jakplugg/Orgone-accumulator/orgone_accumulator/orgone_accumulator_2.0/orgone_accumulator_2.0.ino

/*
Copyright (c) <2016> <James L Matheson>

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
Neutron-sound.com
Orgone Accumulator 2.0
*/
//use 144mhz version, this version is no longer updated.

//pre 2.0 firmware orgones
//use config.h tab to change FX function button to momentary if you changed it.
//tune lock is now pulsar mode. you can change it back in config, but you get no pulsar mode.

//detune = FX
//detune prime = FX select
//detune enable = FX enable
//lock = pulsar

#include <stdint.h>
#include <Bounce.h>
#include <EEPROM.h>
#include "config.h"
#include <Arduino.h>

const float equalTemprementTable[] = {1, 1, 1.05946, 1.12246, 1.18921, 1.25992, 1.33483, 1.41421, 1.49831, 1.58740, 1.68179, 1.78180, 1.88775, 2};
const float justTable[] = {1, 1, 1.0417, 1.1250, 1.2, 1.25, 1.33333, 1.4063, 1.5, 1.6, 1.66666, 1.8, 1.875, 2};

const uint8_t smoothStepTable[] ={ 0,1,1,3,3,5,5,7,7,9,9,11,11,13,13,15};

const uint16_t HARM_LEVELS[] = { //for spectrum FX each row of 9 must add to around 4095 they are ROOT FIFTH OCTAVE 3RDHARM 4thHARM 5thHARM 6thHARM 7thHARM 8thHARM
  2047, 1027, 509, 257, 127, 65, 31, 17, 5, //used odd numbers because the number also determines the detune rate for that oscillator.
  2047, 255, 1027, 125, 509, 0, 0, 231, 512, //octaves
  2040, 0, 0, 0, 1023, 513, 511, 0, 7,
  1023, 0, 0, 0, 0, 1024, 1025, 1021, 0,
  1023, 0, 767, 511, 385, 255, 0, 129, 126,
  701, 102, 712, 256, 507, 64, 0, 511, 253,
  2048, 7, 15, 32, 65, 123, 255, 512, 1021,
  2047, 1024, 0, 1024, 0, 0, 0, 0, 0,
  1847, 1022, 0, 0, 1021, 64, 0, 62, 61,
  2047, 69, 2055, 67, 65, 64, 0, 62, 61,
  2047, 69, 68, 2041, 65, 64, 0, 62, 61,
  2047, 69, 68, 67, 2035, 64, 0, 62, 61,
  0, 0, 0, 0, 1020, 1021, 0, 1023, 1022,
  320, 1241, 321, 735, 1035, 0, 0, 0, 561,
  1803, 0, 168, 0, 504, 0, 1020, 0, 501,
  1703, 251, 0, 502, 307, 201, 0, 1001, 126,
};

const int16_t sinTable[] = {
  0, 402, 804, 1206, 1607, 2009, 2410, 2811, 3211, 3611, 4011, 4409, 4807, 5205, 5601, 5997, 6392,
  6786, 7179, 7571, 7961, 8351, 8739, 9126, 9511, 9895, 10278, 10659, 11038, 11416, 11792, 12166, 12539,
  12909, 13278, 13645, 14009, 14372, 14732, 15090, 15446, 15799, 16150, 16499, 16845, 17189, 17530, 17868, 18204,
  18537, 18867, 19194, 19519, 19840, 20159, 20474, 20787, 21096, 21402, 21705, 22004, 22301, 22594, 22883, 23169,
  23452, 23731, 24006, 24278, 24546, 24811, 25072, 25329, 25582, 25831, 26077, 26318, 26556, 26789, 27019, 27244,
  27466, 27683, 27896, 28105, 28309, 28510, 28706, 28897, 29085, 29268, 29446, 29621, 29790, 29955, 30116, 30272,
  30424, 30571, 30713, 30851, 30984, 31113, 31236, 31356, 31470, 31580, 31684, 31785, 31880, 31970, 32056, 32137,
  32213, 32284, 32350, 32412, 32468, 32520, 32567, 32609, 32646, 32678, 32705, 32727, 32744, 32757, 32764, 32767,
  32764, 32757, 32744, 32727, 32705, 32678, 32646, 32609, 32567, 32520, 32468, 32412, 32350, 32284, 32213, 32137,
  32056, 31970, 31880, 31785, 31684, 31580, 31470, 31356, 31236, 31113, 30984, 30851, 30713, 30571, 30424, 30272,
  30116, 29955, 29790, 29621, 29446, 29268, 29085, 28897, 28706, 28510, 28309, 28105, 27896, 27683, 27466, 27244,
  27019, 26789, 26556, 26318, 26077, 25831, 25582, 25329, 25072, 24811, 24546, 24278, 24006, 23731, 23452, 23169,
  22883, 22594, 22301, 22004, 21705, 21402, 21096, 20787, 20474, 20159, 19840, 19519, 19194, 18867, 18537, 18204,
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
    -30069,-29844,-29613,-29374,-29130,-28878,-28617,-28353,-28078,-27797,-27510,-27215,-26912,-26602,-26284,-25957,
    -25623,-25279,-24927,-24564,-24193,-23811,-23417,-23012,-22595,-22165,-21721,-21261,-20786,-20294,-19784,-19259,
    -18724,-18186,-17653,-17128,-16618,-16122,-15645,-15188,-14748,-14326,-13923,-13535,-13164,-12808,-12466,-12138,
    -11821,-11518,-11224,-10941,-10667,-10403,-10148,-9900,-9660,-9427,-9202,-8983,-8771,-8564,-8363,-8166,
    -7975,-7789,-7607,-7429,-7255,-7086,-6920,-6758,-6599,-6442,-6290,-6141,-5994,-5848,-5706,-5566,
    -5429,-5294,-5161,-5028,-4899,-4771,-4645,-4521,-4398,-4276,-4156,-4037,-3918,-3802,-3686,-3571,
    -3457,-3344,-3231,-3120,-3009,-2898,-2788,-2679,-2569,-2461,-2352,-2242,-2135,-2028,-1919,-1811,
    -1703,-1595,-1486,-1378,-1268,-1159,-1049,-939,-828,-718,-605,-491,-378,-263,-150,-30
};
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
