jakplugg/Orgone-accumulator/orgone_accumulator/orgone_accumulator_2.0/ASSIGNINCREMENTS.ino

void INCREMENT_PWM(){
  oSQ.phase_increment = (inputConverter / PWM_Div) * 4;
  oSQ.PW = (constrain(((FMIndexCont + (1024-(aInModIndex>>2))) ), 0, (2047-PWM_Min)))<<4;
}

void ASSIGNINCREMENTS() { //--------------------------------------------------------default

  CZMix = constrain((FMIndexCont + (2047 - (averageaInIAv / 2.0))), 0, 2047); 
  INCREMENT_PWM();
  switch (oscMode) { //switches which oscs get changed by FM and how much multiplier ;
    case 0://break intentionally ommited

      UPDATECONTROLS_FM();


      FMIndexContCubing = FMIndexCont / 256.0;
      FMIndex = (uint32_t((float)(((FMIndexContCubing * FMIndexContCubing * FMIndexContCubing) + (averageaInIAvCubing * averageaInIAvCubing * averageaInIAvCubing)) * (inputVOct / 2.0))));

      if (averageaInRAv > 4095) {
        ModRatioCubing = (averageaInRAv - 4095.0) / 256.0;
        aInModRatio = ((ModRatioCubing * ModRatioCubing * ModRatioCubing) / 2048.0) + 1.0;
      }
      else aInModRatio = (averageaInRAv / 4096.0); //down direction dont go past zero, or divide by zero could happen

      if (FMFixedOn) {
        avgcubing = (float)(averageratio / 500.0); //change to adjust "LFO" in fm fixed
        FMMult = ((((float)(avgcubing * avgcubing * avgcubing))) + 0.001) * (aInModRatio * 8.0); //FM+fixed mult control
        //Serial.println(FMMult);
        osc_mult[0] = FMMult;
        osc_mult[1] = 4.0;
        o2.phase_increment = inputConverter * osc_mult[1]  ;
        o4.phase_increment = (inputConverter  * chord[0] * osc_mult[1]) + detune[0];
        o6.phase_increment = (inputConverter  * chord[1] * osc_mult[1]) + detune[1];
        o8.phase_increment = (inputConverter * chord[2] * osc_mult[1]) + detune[2];
        o10.phase_increment =(inputConverter * chord[3] * osc_mult[1]) + detune[3];
        o1.phase_increment = inputConverterF * osc_mult[0] ;
        o3.phase_increment = (inputConverterF   * osc_mult[0])  + detune[0];
        o5.phase_increment = (inputConverterF   * osc_mult[0])  + detune[1];
        o7.phase_increment = (inputConverterF  * osc_mult[0])  + detune[2];
        o9.phase_increment = (inputConverterF   * osc_mult[0])  + detune[3];
        //lfo.phase_increment = inputConverterF * (osc_mult[0] / 8.0);
      }
      else {
        FMMult = ((int)((averageratio >> 8) + 1))/2.0 * aInModRatio; //FM + free
        osc_mult[0] = FMMult;
        osc_mult[1] = 4.0;
        o2.phase_increment = inputConverter * osc_mult[1]  ;
        o4.phase_increment = ((inputConverter ) * chord[0] * osc_mult[1]) + detune[0];
        o6.phase_increment = ((inputConverter ) * chord[1] * osc_mult[1]) + detune[1];
        o8.phase_increment = ((inputConverter ) * chord[2] * osc_mult[1]) + detune[2];
        o10.phase_increment = (( inputConverter) * chord[3] * osc_mult[1]) + detune[3];
        o1.phase_increment = inputConverter * osc_mult[0] ;
        o3.phase_increment = (inputConverter  * chord[0] * osc_mult[0])  + detune[0];
        o5.phase_increment = (inputConverter  * chord[1] * osc_mult[0])  + detune[1];
        o7.phase_increment = (inputConverter  * chord[2] * osc_mult[0])  + detune[2];
        o9.phase_increment = (inputConverter  * chord[3] * osc_mult[0])  + detune[3];
        //lfo.phase_increment = inputConverter * (osc_mult[0] / 4.0);
      }
      break;



    case 2://fm mode with x button pressed allows pitch bending on hi position and FM is LFO in fixed (no auto get freq).


      UPDATECONTROLS_FMALT();


      FMIndexContCubing = FMIndexCont / 256.0;
      FMIndex = (uint32_t((float)(((FMIndexContCubing * FMIndexContCubing * FMIndexContCubing) + (averageaInIAvCubing * averageaInIAvCubing * averageaInIAvCubing)) * (inputVOct/2.0))));

      if (averageaInRAv > 4095) {
        ModRatioCubing = (averageaInRAv - 4095) / 256.0;
        aInModRatio = ((ModRatioCubing * ModRatioCubing * ModRatioCubing) / 512.0) + 1.0;
      }
      else aInModRatio = (averageaInRAv / 4096.0); //down direction dont go past zero, or divide by zero could happen


      if (FMFixedOn) {
        float avgcubing = averageratio / 500.0; //change to adjust "LFO" in fm fixed
        FMMult = ((((float)(avgcubing * avgcubing * avgcubing))) + 0.001) * (aInModRatio * 8.0); //FM+fixed mult control
        osc_mult[0] = FMMult;
        osc_mult[1] = 4;
        FMX_HiOffset = (float)(1.0 + (mixHi * FMX_HiOffsetCont)/2048.0);
        o2.phase_increment = inputConverter * osc_mult[1] * FMX_HiOffset ;
        o4.phase_increment = inputConverter * chord[0]  * osc_mult[1] * FMX_HiOffset + detune[0] ;
        o6.phase_increment = inputConverter  * chord[1] * osc_mult[1]  * FMX_HiOffset + detune[1] ;
        o8.phase_increment = inputConverter  * chord[2] * osc_mult[1] * FMX_HiOffset + detune[2] ;
        o10.phase_increment = inputConverter * chord[3] * osc_mult[1] * FMX_HiOffset + detune[3] ;
        o1.phase_increment = inputConverterF  * osc_mult[0] ;
        o3.phase_increment = inputConverterF  * osc_mult[0] ;
        o5.phase_increment = inputConverterF * osc_mult[0] ;
        o7.phase_increment = inputConverterF * osc_mult[0] ;
        o9.phase_increment = inputConverterF * osc_mult[0] ;
        //lfo.phase_increment = inputConverterF * (osc_mult[0] / 8.0);
      }
      else {
        FMMult = ((int)((averageratio >> 9) + 1)) * aInModRatio; //FM + free
        osc_mult[0] = FMMult;
        osc_mult[1] = 4;
        FMX_HiOffset = (float)(1.0 + ((float)(mixHi) * FMX_HiOffsetCont)/2048.0);
        o2.phase_increment = inputConverter * osc_mult[1] * FMX_HiOffset ;
        o4.phase_increment = inputConverter * osc_mult[1] * chord[0] * FMX_HiOffset+ detune[0] ;
        o6.phase_increment = inputConverter * osc_mult[1] * chord[1] * FMX_HiOffset  + detune[1] ;
        o8.phase_increment = inputConverter * osc_mult[1] * chord[2] * FMX_HiOffset + detune[2] ;
        o10.phase_increment = inputConverter * osc_mult[1] * chord[3] * FMX_HiOffset + detune[3] ;
        o1.phase_increment = inputConverter * osc_mult[0] ;
        o3.phase_increment = inputConverter * osc_mult[0]  + detune[0];
        o5.phase_increment = inputConverter * osc_mult[0]  + detune[1];
        o7.phase_increment = inputConverter * osc_mult[0]  + detune[2];
        o9.phase_increment = inputConverter * osc_mult[0]  + detune[3];
        //lfo.phase_increment = inputConverter * (osc_mult[0] / 4.0);
      }
      break;
    case 1://cz

      UPDATECONTROLS_CZ();

      if (averageaInRAv > 4095) {
        ModRatioCubing = (averageaInRAv - 4095) / 256.0;
        aInModRatio = ((ModRatioCubing * ModRatioCubing * ModRatioCubing) / 2048.0) + 1.0;
      }
      else aInModRatio = (averageaInRAv / 4096.0); //down direction dont go past zero, or divide by zero could happen


      if (FMFixedOn) {
        FMMult = (float)((((averageratio >> 3) / 1.1)) + 1.0) * aInModRatio; 
        osc_mult[0] = 4;
        osc_mult[1] = FMMult;
       
        o1.phase_increment = inputConverter * osc_mult[0];
        o3.phase_increment = inputConverter * chord[0] * osc_mult[0] + detune[0];
        o5.phase_increment = inputConverter * chord[1] * osc_mult[0] + detune[1];
        o7.phase_increment = inputConverter * chord[2] * osc_mult[0] + detune[2];
        o9.phase_increment = inputConverter * chord[3] * osc_mult[0] + detune[3];
         o2.phase_increment =
          o4.phase_increment =
            o6.phase_increment =
              o8.phase_increment =
                o10.phase_increment = inputConverterA * osc_mult[1];
      }
      else {
        FMMult = (float)((((averageratio >> 5) / 7.0)) + 1.0) * aInModRatio; 
        osc_mult[0] = 4;
        osc_mult[1] = FMMult;        
        o2.phase_increment = inputConverter * osc_mult[1];
        o4.phase_increment = o2.phase_increment  * chord[0] + detune[0];
        o6.phase_increment = o2.phase_increment * chord[1] + detune[1];
        o8.phase_increment = o2.phase_increment  * chord[2] + detune[2];
        o10.phase_increment = o2.phase_increment  * chord[3] + detune[3];
        o1.phase_increment = inputConverter * osc_mult[0];
        o3.phase_increment = o1.phase_increment  * chord[0] + detune[0];
        o5.phase_increment = o1.phase_increment  * chord[1] + detune[1];
        o7.phase_increment = o1.phase_increment  * chord[2] + detune[2];
        o9.phase_increment = o1.phase_increment  * chord[3] + detune[3];
      }
      break;


    case 3://ALT CZ


      UPDATECONTROLS_CZALT();

     if (averageaInRAv > 4095) {
        ModRatioCubing = (averageaInRAv - 4095) / 256.0;
        aInModRatio = ((ModRatioCubing * ModRatioCubing * ModRatioCubing) / 2048.0) + 1.0;
      }
      else aInModRatio = (averageaInRAv / 4096.0); //down direction dont go past zero, or divide by zero could happen



      if (FMFixedOn) {
        FMMult = (float)((((averageratio >> 3) / 1.1)) + 1.0) * aInModRatio; //CZ + fixed + free
        osc_mult[0] = 4;
        osc_mult[1] = FMMult;
        FMX_HiOffset = (float)(1.0 + ((float)(mixHi) * FMX_HiOffsetCont)/2048.0);
        o2.phase_increment =  inputConverterA * osc_mult[1]*FMX_HiOffset;
        o4.phase_increment =  inputConverterA * chord[0] * osc_mult[1]*FMX_HiOffset;
        o6.phase_increment =  inputConverterA * chord[1] * osc_mult[1]*FMX_HiOffset;
        o8.phase_increment =  inputConverterA * chord[2] * osc_mult[1]*FMX_HiOffset;
        o10.phase_increment = inputConverterA * chord[3] * osc_mult[1]*FMX_HiOffset;
        o1.phase_increment = inputConverter * osc_mult[0]*FMX_HiOffset;
        o3.phase_increment = inputConverter * chord[0] * osc_mult[0]*FMX_HiOffset + detune[0];
        o5.phase_increment = inputConverter * chord[1] * osc_mult[0]*FMX_HiOffset + detune[1];
        o7.phase_increment = inputConverter * chord[2] * osc_mult[0]*FMX_HiOffset + detune[2];
        o9.phase_increment = inputConverter * chord[3] * osc_mult[0]*FMX_HiOffset + detune[3];
        lfo.phase_increment = inputConverterF * (osc_mult[1] / 8.0);
      }
      else {
        FMMult = (float)((((averageratio >> 5) / 7.0)) + 1.0) * aInModRatio;
        osc_mult[0] = 4;
        osc_mult[1] = FMMult;
        FMX_HiOffset = (float)(1.0 + ((float)(mixHi) * FMX_HiOffsetCont)/2048.0);
        o2.phase_increment = inputConverter * osc_mult[1];
        o4.phase_increment = o2.phase_increment  * chord[0] + detune[0];
        o6.phase_increment = o2.phase_increment * chord[1] + detune[1];
        o8.phase_increment = o2.phase_increment  * chord[2] + detune[2];
        o10.phase_increment = o2.phase_increment  * chord[3] + detune[3];
        o1.phase_increment = inputConverter * osc_mult[0]*FMX_HiOffset;
        o3.phase_increment = o1.phase_increment  * chord[0]*FMX_HiOffset + detune[0];
        o5.phase_increment = o1.phase_increment  * chord[1]*FMX_HiOffset + detune[1];
        o7.phase_increment = o1.phase_increment  * chord[2]*FMX_HiOffset + detune[2];
        o9.phase_increment = o1.phase_increment  * chord[3]*FMX_HiOffset + detune[3];
        lfo.phase_increment = inputConverter * (osc_mult[1] / 4.0);
      }

      break;

  }
}


void ASSIGNINCREMENTS_P() { //--------------------------------------------for pulsar

  PENV = PulsarEnv[analogControls[3] >> 9];

  FMIndexContCubing = FMIndexCont / 256.0;
   INCREMENT_PWM();
  switch (oscMode) { //switches which oscs get changed by FM and how much multiplier ;

    case 0:
      UPDATECONTROLS_FM();
       o1.phase_SUB = inputConverter * 1;
      FMX_HiOffset = 1;
      FMIndex = (uint32_t((float)(((FMIndexContCubing * FMIndexContCubing * FMIndexContCubing) + (averageaInIAvCubing * averageaInIAvCubing * averageaInIAvCubing)) * (inputVOct / 2.0))));
      break;
    case 1:
      UPDATECONTROLS_CZ();
      
      o1.phase_SUB = 0;
      FMX_HiOffset = 1;
      FMIndex = 0;
      break;
    case 2:
      UPDATECONTROLS_FMALT();
      o1.phase_SUB = inputConverter * 1;
      FMX_HiOffset = (float)(1.0 + ((float)(mixHi) * FMX_HiOffsetCont)/2048.0);
      FMIndex = (uint32_t((float)(((FMIndexContCubing * FMIndexContCubing * FMIndexContCubing) + (averageaInIAvCubing * averageaInIAvCubing * averageaInIAvCubing)) * (inputVOct / 2.0))));
      break;
    case 3:
      UPDATECONTROLS_CZALT();
      
      o1.phase_SUB = 0;
      FMX_HiOffset = (float)(1.0 + ((float)(mixHi) * FMX_HiOffsetCont)/2048.0);
      FMIndex = 0;
      break;
  }

  CZMix = 2047-(constrain((FMIndexCont + (2047 - (averageaInIAv / 2.0))), 0, 2020));//reverse control and offset pulse envelope length
  

  if (averageaInRAv > 4095) {
    ModRatioCubing = (averageaInRAv - 4095) / 256.0;
    aInModRatio = ((ModRatioCubing * ModRatioCubing * ModRatioCubing) / 512.0) + 1.0;
  }
  else aInModRatio = (averageaInRAv / 4096.0); 

  
   if (FMmodeOn){
  if (FMFixedOn) {
    
    if (FX == 6) FMMult = (float)((((analogControls[3]) * 1.5 )) + 1.0);
    else FMMult = (float)((((averageratio) >>1 )) + 1.0) * aInModRatio;
    osc_mult[0] = 4;
    osc_mult[1] = FMMult;
    osc_mult[2] = 4;

       
    o1.pulseAdd = (inputConverterF * osc_mult[2]) * (float)(CZMix / 6.0);

    o1.phase_increment = inputConverter * osc_mult[0] * FMX_HiOffset;
    o2.phase_increment = inputConverterF * osc_mult[1];
    o3.phase_increment = inputConverterF * osc_mult[2] + o1.pulseAdd;
    if (o1.phase_increment > (o3.phase_increment<<1))o3.phase_increment = o1.phase_increment>>1;//these stop the pulsar envelope getting longer than the pitch.

    o4.phase_increment = inputConverter   * chord[1] * osc_mult[0] * FMX_HiOffset + detune[1];
    o5.phase_increment = inputConverterF * osc_mult[1];
    o6.phase_increment = inputConverterF * osc_mult[2] + o1.pulseAdd;
    if (o4.phase_increment > (o6.phase_increment<<1))o6.phase_increment = o4.phase_increment>>1;

    o7.phase_increment = inputConverter  * chord[2] * osc_mult[0] * FMX_HiOffset + detune[2];
    o8.phase_increment = inputConverterF * osc_mult[1];
    o9.phase_increment = inputConverterF * osc_mult[2] + o1.pulseAdd;
    if (o7.phase_increment > (o9.phase_increment<<1))o9.phase_increment = o7.phase_increment>>1;

    o10.phase_increment = inputConverter  * chord[3] * osc_mult[0] * FMX_HiOffset - detune[3];
    o11.phase_increment = inputConverterF * osc_mult[1];
    o12.phase_increment = inputConverterF * osc_mult[2] + o1.pulseAdd;
    if (o10.phase_increment > (o12.phase_increment<<1))o12.phase_increment = o10.phase_increment>>1;

    
    
   
  }
  else {
    if (FX == 6) FMMult = (float)((((analogControls[3] >> 4) / 14.0)) + 1.0) ;    
    else FMMult = (float)((((averageratio >> 5) / 5.0)) + 1) * aInModRatio;
    osc_mult[0] = 4;
    osc_mult[1] = FMMult;
    osc_mult[2] = 4;

    o1.pulseAdd = (inputConverterF * osc_mult[2]) * (float)(CZMix / 6.0);

    o1.phase_increment = inputConverter * osc_mult[0] * FMX_HiOffset;
    o2.phase_increment = inputConverter * osc_mult[1];
    o3.phase_increment = inputConverterF * osc_mult[2] + o1.pulseAdd;   
     if (o1.phase_increment > (o3.phase_increment<<1))o3.phase_increment = o1.phase_increment>>1;//these stop the pulsar envelope getting longer than the pitch. 

    o4.phase_increment = inputConverter * chord[1] * osc_mult[0] * FMX_HiOffset + detune[1];
    o5.phase_increment = inputConverter * osc_mult[1] + detune[1];
    o6.phase_increment = inputConverterF * osc_mult[2] + o1.pulseAdd;
    if (o4.phase_increment > (o6.phase_increment<<1))o6.phase_increment = o4.phase_increment>>1;

    o7.phase_increment = inputConverter * chord[2] * osc_mult[0] * FMX_HiOffset + detune[2];
    o8.phase_increment = inputConverter * osc_mult[1] + detune[2];
    o9.phase_increment = inputConverterF * osc_mult[2] + o1.pulseAdd;
     if (o7.phase_increment > (o9.phase_increment<<1))o9.phase_increment = o7.phase_increment>>1;

    o10.phase_increment = inputConverter  * chord[3] * osc_mult[0] * FMX_HiOffset + detune[3];
    o11.phase_increment = inputConverter * osc_mult[1]+ detune[3];
    o12.phase_increment = inputConverterF * osc_mult[2] + o1.pulseAdd;
    if (o10.phase_increment > (o12.phase_increment<<1))o12.phase_increment = o10.phase_increment>>1;
    
  }
   }
   else{
  if (FMFixedOn) {
    
    if (FX == 6) FMMult = (float)((((analogControls[3]) * 1.5 )) + 1.0);
    else FMMult = (float)((((averageratio) >>1 )) + 1.0) * aInModRatio;
    osc_mult[0] = 4;
    osc_mult[1] = FMMult;
    osc_mult[2] = 4;

     o1.pulseAdd = (inputConverter * osc_mult[2]) * (float)(CZMix / 255.0);

    o1.phase_increment = inputConverter * osc_mult[0] * FMX_HiOffset;
    o2.phase_increment = inputConverterF * osc_mult[1];
    o3.phase_increment = inputConverter * osc_mult[2] + o1.pulseAdd;

    o4.phase_increment = inputConverter   * chord[1] * osc_mult[0] * FMX_HiOffset + detune[1];
    o5.phase_increment = inputConverterF * osc_mult[1];
    o6.phase_increment = inputConverter * osc_mult[2] + o1.pulseAdd;

    o7.phase_increment = inputConverter  * chord[2] * osc_mult[0] * FMX_HiOffset + detune[2];
    o8.phase_increment = inputConverterF * osc_mult[1];
    o9.phase_increment = inputConverter * osc_mult[2] + o1.pulseAdd;

    o10.phase_increment = inputConverter  * chord[3] * osc_mult[0] * FMX_HiOffset + detune[3];
    o11.phase_increment = inputConverterF * osc_mult[1];
    o12.phase_increment = inputConverter * osc_mult[2] + o1.pulseAdd;

    //o1.pulseAdd = o3.phase_increment * (float)((CZMix / 255.0));
   
  }
  else {
    if (FX == 6) FMMult = (float)((((analogControls[3] >> 4) / 14.0)) + 1.0) ;    
    else FMMult = (float)((((averageratio >> 5) / 10.0)) + 1.0) * aInModRatio;
    osc_mult[0] = 4;
    osc_mult[1] = FMMult;
    osc_mult[2] = 4;

    o1.pulseAdd = (inputConverter * osc_mult[2]) * (float)(CZMix / 255.0);

    o1.phase_increment = inputConverter * osc_mult[0] * FMX_HiOffset;
    o2.phase_increment = inputConverter * osc_mult[1];
    o3.phase_increment = inputConverter * osc_mult[2]+ o1.pulseAdd;    

    o4.phase_increment = inputConverter * chord[1] * osc_mult[0] * FMX_HiOffset + detune[1];
    o5.phase_increment = inputConverter * osc_mult[1] + detune[1];
    o6.phase_increment = inputConverter * osc_mult[2]+ o1.pulseAdd;

    o7.phase_increment = inputConverter * chord[2] * osc_mult[0] * FMX_HiOffset + detune[2];
    o8.phase_increment = inputConverter * osc_mult[1] + detune[2];
    o9.phase_increment = inputConverter * osc_mult[2]+ o1.pulseAdd;

     o10.phase_increment = inputConverter * chord[3] * osc_mult[0] * FMX_HiOffset + detune[3];
    o11.phase_increment = inputConverter * osc_mult[1] + detune[3];
    o12.phase_increment = inputConverter * osc_mult[2]+ o1.pulseAdd;

    //o1.pulseAdd =  o3.phase_increment * (float)((CZMix / 255.0));         
    
  }
   }
 
}
void ASSIGNINCREMENTS_D() { //--------------------------------------------------------delay


  CZMix = constrain((FMIndexCont + (2047 - (averageaInIAv / 2.0))), 0, 2047);
   INCREMENT_PWM();
  if (averageaInRAv > 4095) {
    ModRatioCubing = (averageaInRAv - 4095.0) / 256.0;
    aInModRatio = ((ModRatioCubing * ModRatioCubing * ModRatioCubing) / 2048.0) + 1.0;
  }
  else aInModRatio = (averageaInRAv / 4096.0); //down direction dont go past zero, or divide by zero could happen


  switch (oscMode) {
    case 0:

      UPDATECONTROLS_FM();

      FMIndexContCubing = FMIndexCont / 256.0;
      FMIndex = (uint32_t((float)(((FMIndexContCubing * FMIndexContCubing * FMIndexContCubing) + (averageaInIAvCubing * averageaInIAvCubing * averageaInIAvCubing)) * (inputVOct / 2.0))));


      if (FMFixedOn) {
        avgcubing = (float)(analogControls[3] / 500.0); //change to adjust "LFO" in fm fixed
        FMMult = ((((float)(avgcubing * avgcubing * avgcubing))) + 0.001); 
        //Serial.println(FMMult);
        osc_mult[0] = FMMult;
        osc_mult[1] = 4.0;
        o1.phase_increment = inputConverterF * osc_mult[0] ;
        o2.phase_increment = inputConverter * osc_mult[1]  ;
   

      }
      else {
        FMMult = ((int)((analogControls[3] >> 9) + 1)); 
        osc_mult[0] = FMMult;
        osc_mult[1] = 4.0;
        o1.phase_increment = inputConverter * osc_mult[0] ;
        o2.phase_increment = inputConverter * osc_mult[1] ;
 
      }
      break;

    case 2://fm mode with x button pressed allows pitch bending on hi position and FM is LFO in fixed (no auto get freq).

      UPDATECONTROLS_FMALT();

      FMIndexContCubing = FMIndexCont / 256.0;
      FMIndex = (uint32_t((float)(((FMIndexContCubing * FMIndexContCubing * FMIndexContCubing) + (averageaInIAvCubing * averageaInIAvCubing * averageaInIAvCubing)) * (inputVOct / 2.0))));

FMX_HiOffset = (float)(1.0 + ((float)(mixHi) * FMX_HiOffsetCont)/2048.0);
    
      if (FMFixedOn) {
        float avgcubing = analogControls[3] / 500.0; //change to adjust "LFO" in fm fixed
        FMMult = ((((float)(avgcubing * avgcubing * avgcubing))) + 0.001); //FM+fixed mult control
        osc_mult[0] = FMMult;
        osc_mult[1] = 4;
        
        o1.phase_increment = inputConverterF * osc_mult[0] ;
        o2.phase_increment = inputConverter * osc_mult[1] * FMX_HiOffset ;
 

      }
      else {
        FMMult = ((int)((analogControls[3] >> 9) + 1)); 
        osc_mult[0] = FMMult;
        osc_mult[1] = 4;
        
        o1.phase_increment = inputConverter * osc_mult[0] ;
        o2.phase_increment = inputConverter * osc_mult[1] * FMX_HiOffset ;
 

      }
      break;
    case 1://cz

      UPDATECONTROLS_CZ();

      if (FMFixedOn) {
        FMMult = (float)((((analogControls[3] >> 3) / 1.1)) + 1.0); //CZ + fixed + free
        osc_mult[0] = 4;
        osc_mult[1] = FMMult;
        o1.phase_increment = inputConverter * osc_mult[0];
        o2.phase_increment = inputConverterF * osc_mult[1];
     
      }
      else {
        FMMult = (float)((((analogControls[3] >> 5))) + 1.0); //CZ + free + free
        osc_mult[0] = 4;
        osc_mult[1] = FMMult;
        o1.phase_increment = inputConverter * osc_mult[0];
        o2.phase_increment = inputConverter * osc_mult[1];
   

      }
      break;


    case 3://ALT CZ

      UPDATECONTROLS_CZALT();
FMX_HiOffset = (float)(1.0 + ((float)(mixHi) * FMX_HiOffsetCont)/2048.0);

      if (FMFixedOn) {
        FMMult = (float)((((analogControls[3] >> 3) / 1.1)) + 1.0); 
        osc_mult[0] = 4;
        osc_mult[1] = FMMult;
        
        o2.phase_increment = inputConverterF * osc_mult[1] ; //modulation not detuned
        o1.phase_increment = inputConverter * osc_mult[0] *FMX_HiOffset;    
       
        lfo.phase_increment = inputConverterF * (osc_mult[1] / 8.0);
      }
      else {
        FMMult = (float)((((analogControls[3] >> 5))) + 1.0); //CZ + free + free
        osc_mult[0] = 4;
        osc_mult[1] = FMMult;
        
        o2.phase_increment = inputConverter * osc_mult[1];
        o1.phase_increment = inputConverter * osc_mult[0] * FMX_HiOffset;
       
        lfo.phase_increment = inputConverter * (osc_mult[1] / 2.0);
       
      }
      break;
  }
}


void ASSIGNINCREMENTS_DRUM() { //--------------------------------------------------------drum effect
 INCREMENT_PWM();
  UPDATECONTROLS_DRUM();
  //    Serial.print   (CZMix);
  //    Serial.print   ("      ");
  //Serial.println(inputConverter);

  //CZMix = constrain(((FMIndexCont) + (2047 - (averageaInIAv / 2.0))), 0, 2047); 
  CZMix = envVal>>1;

  
  if (FMFixedOn) {
    osc_mult[0] = 250.0;
    osc_mult[1] = 4.0;
    o1.phase_increment = inputConverter * osc_mult[1]  ;
    o2.phase_increment = inputConverterF * osc_mult[0] * chord[0];
    o3.phase_increment = inputConverterF * osc_mult[0] * chord[1];
    o4.phase_increment = inputConverterF * osc_mult[0] * chord[2];
    o5.phase_increment = inputConverterF * osc_mult[0] * chord[3];
  }
  else {
    FMMult = ((int)((averageratio >> 9) + 1)) * aInModRatio; //FM + free
    osc_mult[0] = FMMult;
    osc_mult[1] = 4.0;
    o1.phase_increment = inputConverter * osc_mult[1]  ;
    o2.phase_increment = (inputConverter * osc_mult[1]) * chord[0];
    o3.phase_increment = (inputConverter * osc_mult[1]) * chord[1];
    o4.phase_increment = (inputConverter * osc_mult[1]) * chord[2];
    o5.phase_increment = (inputConverter * osc_mult[1]) * chord[3];
  }
}

void ASSIGNINCREMENTS_SPECTRUM() { //--------------------------------------------------------

  PENV = PulsarEnv[analogControls[3] >> 9];
 INCREMENT_PWM();
  CZMix = constrain((FMIndexCont + (2047 - (averageaInIAv / 2.0))), 0, 2047);

  if (averageaInRAv > 4095) {
    ModRatioCubing = (averageaInRAv - 4095.0) / 256.0;
    aInModRatio = ((ModRatioCubing * ModRatioCubing * ModRatioCubing) / 2048.0) + 1.0;
  }
  else aInModRatio = (averageaInRAv / 4096.0); //down direction dont go past zero, or divide by zero could happen

  switch (oscMode) { //switches which oscs get changed by FM and how much multiplier ;
    case 0://break intentionally ommited

      UPDATECONTROLS_FM();

      o2.index = (((HARM_LEVELS[Lbuh]) * mixLo) + ((HARM_LEVELS[Mbuh]) * mixMid) + ((HARM_LEVELS[Hbuh]) * mixHi)) >> 11;
      o3.index = (((HARM_LEVELS[1 + Lbuh]) * mixLo) + ((HARM_LEVELS[1 + Mbuh]) * mixMid) + ((HARM_LEVELS[1 + Hbuh]) * mixHi)) >> 11;
      o4.index = (((HARM_LEVELS[2 + Lbuh]) * mixLo) + ((HARM_LEVELS[2 + Mbuh]) * mixMid) + ((HARM_LEVELS[2 + Hbuh]) * mixHi)) >> 11;
      o5.index = (((HARM_LEVELS[3 + Lbuh]) * mixLo) + ((HARM_LEVELS[3 + Mbuh]) * mixMid) + ((HARM_LEVELS[3 + Hbuh]) * mixHi)) >> 11;
      o6.index = (((HARM_LEVELS[4 + Lbuh]) * mixLo) + ((HARM_LEVELS[4 + Mbuh]) * mixMid) + ((HARM_LEVELS[4 + Hbuh]) * mixHi)) >> 11;
      o7.index = (((HARM_LEVELS[5 + Lbuh]) * mixLo) + ((HARM_LEVELS[5 + Mbuh]) * mixMid) + ((HARM_LEVELS[5 + Hbuh]) * mixHi)) >> 11;
      o8.index = (((HARM_LEVELS[6 + Lbuh]) * mixLo) + ((HARM_LEVELS[6 + Mbuh]) * mixMid) + ((HARM_LEVELS[6 + Hbuh]) * mixHi)) >> 11;
      o9.index = (((HARM_LEVELS[7 + Lbuh]) * mixLo) + ((HARM_LEVELS[7 + Mbuh]) * mixMid) + ((HARM_LEVELS[7 + Hbuh]) * mixHi)) >> 11;
      o10.index = (((HARM_LEVELS[8 + Lbuh]) * mixLo) + ((HARM_LEVELS[8 + Mbuh]) * mixMid) + ((HARM_LEVELS[8 + Hbuh]) * mixHi)) >> 11;


      FMIndexContCubing = FMIndexCont / 256.0;
      FMIndex = (uint32_t((float)(((FMIndexContCubing * FMIndexContCubing * FMIndexContCubing) + (averageaInIAvCubing * averageaInIAvCubing * averageaInIAvCubing)) * (inputVOct / 2.0))));


      if (FMFixedOn) {
        avgcubing = (float)(averageratio / 500.0); //change to adjust "LFO" in fm fixed
        FMMult = ((((float)(avgcubing * avgcubing * avgcubing))) + 0.001) * (aInModRatio * 8.0); //FM+fixed mult control
        //Serial.println(FMMult);
        osc_mult[0] = FMMult;
      }
      else {
        FMMult = ((int)((averageratio >> 9) + 1)) * aInModRatio; //FM + free
        osc_mult[0] = FMMult;
      }

      FMX_HiOffset = 1;
      break;

    case 2://fm mode with x button pressed allows pitch bending on hi position and FM is LFO in fixed (no auto get freq).

      UPDATECONTROLS_FMALT();

      o2.index = (((HARM_LEVELS[Lbuh]) * mixLo) + ((HARM_LEVELS[Mbuh]) * (mixMid + mixHi))) >> 11;
      o3.index = (((HARM_LEVELS[1 + Lbuh]) * mixLo) + ((HARM_LEVELS[1 + Mbuh]) * (mixMid + mixHi))) >> 11;
      o4.index = (((HARM_LEVELS[2 + Lbuh]) * mixLo) + ((HARM_LEVELS[2 + Mbuh]) * (mixMid + mixHi))) >> 11;
      o5.index = (((HARM_LEVELS[3 + Lbuh]) * mixLo) + ((HARM_LEVELS[3 + Mbuh]) * (mixMid + mixHi))) >> 11;
      o6.index = (((HARM_LEVELS[4 + Lbuh]) * mixLo) + ((HARM_LEVELS[4 + Mbuh]) * (mixMid + mixHi))) >> 11;
      o7.index = (((HARM_LEVELS[5 + Lbuh]) * mixLo) + ((HARM_LEVELS[5 + Mbuh]) * (mixMid + mixHi))) >> 11;
      o8.index = (((HARM_LEVELS[6 + Lbuh]) * mixLo) + ((HARM_LEVELS[6 + Mbuh]) * (mixMid + mixHi))) >> 11;
      o9.index = (((HARM_LEVELS[7 + Lbuh]) * mixLo) + ((HARM_LEVELS[7 + Mbuh]) * (mixMid + mixHi))) >> 11;
      o10.index = (((HARM_LEVELS[8 + Lbuh]) * mixLo) + ((HARM_LEVELS[8 + Mbuh]) * (mixMid + mixHi))) >> 11;


      FMIndexContCubing = FMIndexCont / 256.0;
      FMIndex = (uint32_t((float)(((FMIndexContCubing * FMIndexContCubing * FMIndexContCubing) + (averageaInIAvCubing * averageaInIAvCubing * averageaInIAvCubing)) * (inputVOct / 2.0))));

      FMX_HiOffset = (float)(1.0 + ((float)(mixHi) * FMX_HiOffsetCont)/2048.0);
      
      if (FMFixedOn) {
        float avgcubing = averageratio / 500.0; //change to adjust "LFO" in fm fixed
        FMMult = ((((float)(avgcubing * avgcubing * avgcubing))) + 0.001) * (aInModRatio * 8.0); //FM+fixed mult control
        osc_mult[0] = FMMult;
      }
      else {
        FMMult = ((int)((averageratio >> 9) + 1)) * aInModRatio; //FM + free
        osc_mult[0] = FMMult;

      }
      break;
    case 1://cz

      UPDATECONTROLS_CZ();

      o2.index = (((HARM_LEVELS[Lbuh]) * mixLo) + ((HARM_LEVELS[Mbuh]) * mixMid) + ((HARM_LEVELS[Hbuh]) * mixHi)) >> 11;
      o3.index = (((HARM_LEVELS[1 + Lbuh]) * mixLo) + ((HARM_LEVELS[1 + Mbuh]) * mixMid) + ((HARM_LEVELS[1 + Hbuh]) * mixHi)) >> 11;
      o4.index = (((HARM_LEVELS[2 + Lbuh]) * mixLo) + ((HARM_LEVELS[2 + Mbuh]) * mixMid) + ((HARM_LEVELS[2 + Hbuh]) * mixHi)) >> 11;
      o5.index = (((HARM_LEVELS[3 + Lbuh]) * mixLo) + ((HARM_LEVELS[3 + Mbuh]) * mixMid) + ((HARM_LEVELS[3 + Hbuh]) * mixHi)) >> 11;
      o6.index = (((HARM_LEVELS[4 + Lbuh]) * mixLo) + ((HARM_LEVELS[4 + Mbuh]) * mixMid) + ((HARM_LEVELS[4 + Hbuh]) * mixHi)) >> 11;
      o7.index = (((HARM_LEVELS[5 + Lbuh]) * mixLo) + ((HARM_LEVELS[5 + Mbuh]) * mixMid) + ((HARM_LEVELS[5 + Hbuh]) * mixHi)) >> 11;
      o8.index = (((HARM_LEVELS[6 + Lbuh]) * mixLo) + ((HARM_LEVELS[6 + Mbuh]) * mixMid) + ((HARM_LEVELS[6 + Hbuh]) * mixHi)) >> 11;
      o9.index = (((HARM_LEVELS[7 + Lbuh]) * mixLo) + ((HARM_LEVELS[7 + Mbuh]) * mixMid) + ((HARM_LEVELS[7 + Hbuh]) * mixHi)) >> 11;
      o10.index = (((HARM_LEVELS[8 + Lbuh]) * mixLo) + ((HARM_LEVELS[8 + Mbuh]) * mixMid) + ((HARM_LEVELS[8 + Hbuh]) * mixHi)) >> 11;


      if (FMFixedOn) {
        FMMult = (float)((((averageratio >> 2) / 1.1)) + 1.0) * aInModRatio; //CZ + fixed + free
        osc_mult[0] = FMMult;
      }
      else {
        FMMult = (float)((((averageratio >> 4) / 5.1)) + 1.0) * aInModRatio;
        osc_mult[0] = FMMult;
      }

      FMX_HiOffset = 1;
      FMIndex = 0;
      break;

    case 3://ALT CZ

      UPDATECONTROLS_CZALT();

      o2.index = (((HARM_LEVELS[Lbuh]) * mixLo) + ((HARM_LEVELS[Mbuh]) * (mixMid + mixHi))) >> 11;
      o3.index = (((HARM_LEVELS[1 + Lbuh]) * mixLo) + ((HARM_LEVELS[1 + Mbuh]) * (mixMid + mixHi))) >> 11;
      o4.index = (((HARM_LEVELS[2 + Lbuh]) * mixLo) + ((HARM_LEVELS[2 + Mbuh]) * (mixMid + mixHi))) >> 11;
      o5.index = (((HARM_LEVELS[3 + Lbuh]) * mixLo) + ((HARM_LEVELS[3 + Mbuh]) * (mixMid + mixHi))) >> 11;
      o6.index = (((HARM_LEVELS[4 + Lbuh]) * mixLo) + ((HARM_LEVELS[4 + Mbuh]) * (mixMid + mixHi))) >> 11;
      o7.index = (((HARM_LEVELS[5 + Lbuh]) * mixLo) + ((HARM_LEVELS[5 + Mbuh]) * (mixMid + mixHi))) >> 11;
      o8.index = (((HARM_LEVELS[6 + Lbuh]) * mixLo) + ((HARM_LEVELS[6 + Mbuh]) * (mixMid + mixHi))) >> 11;
      o9.index = (((HARM_LEVELS[7 + Lbuh]) * mixLo) + ((HARM_LEVELS[7 + Mbuh]) * (mixMid + mixHi))) >> 11;
      o10.index = (((HARM_LEVELS[8 + Lbuh]) * mixLo) + ((HARM_LEVELS[8 + Mbuh]) * (mixMid + mixHi))) >> 11;


      if (FMFixedOn) {
        FMMult = (float)((((averageratio >> 2) / 1.1)) + 1.0) * aInModRatio; //CZ + fixed + free
        osc_mult[0] = FMMult;
      }
      else {
        FMMult = (float)((((averageratio >> 4) / 5.1)) + 1.0) * aInModRatio;
        osc_mult[0] = FMMult;
      }

    FMX_HiOffset = (float)(1.0 + ((float)(mixHi) * FMX_HiOffsetCont)/2048.0);
      FMIndex = 0;
      break;
  }

  if (FMFixedOn){o1.phase_increment = inputConverterF * osc_mult[0] ;
  lfo.phase_increment = inputConverterF * (osc_mult[0] / 20.0);}
  else {o1.phase_increment = inputConverter * osc_mult[0] ;
  lfo.phase_increment = inputConverter * (osc_mult[0] / 4.0);}
  
  o2.phase_increment = inputConverter * 4.0 * FMX_HiOffset ;
  o3.phase_increment = inputConverter * 6.0 * chord[0] * FMX_HiOffset;
  o4.phase_increment = inputConverter * 8.0 * chord[1] * FMX_HiOffset;
  o5.phase_increment = inputConverter * 12.0 * chord[2] * FMX_HiOffset;
  o6.phase_increment = inputConverter * 16.0 * chord[3] * FMX_HiOffset;
  o7.phase_increment = inputConverter * 20.0 *(-chord[0])* FMX_HiOffset;
  o8.phase_increment = inputConverter * 24.0 *(-chord[1])* FMX_HiOffset;
  o9.phase_increment = inputConverter * 28.0 * (-chord[2]) * FMX_HiOffset;
  o10.phase_increment = inputConverter * 32.0* (-chord[3])  * FMX_HiOffset;


}
